atoomnetmarc/yaafr/Kicad/Yet Another AVR Fusebit Rescuer-render.jpg

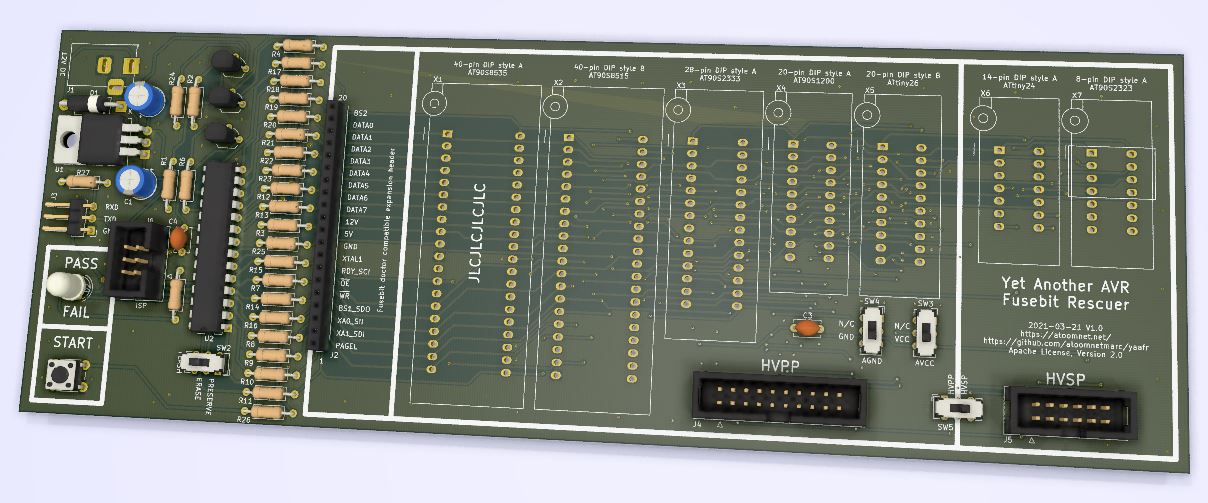
Kicad/Yet Another AVR Fusebit Rescuer-render.jpg
